noelvissers/esp32-smart-clock/hardware/smart-clock-library/3d-files/M3 Spacer Male-Female - 5mm Height x 3mm Thread.step

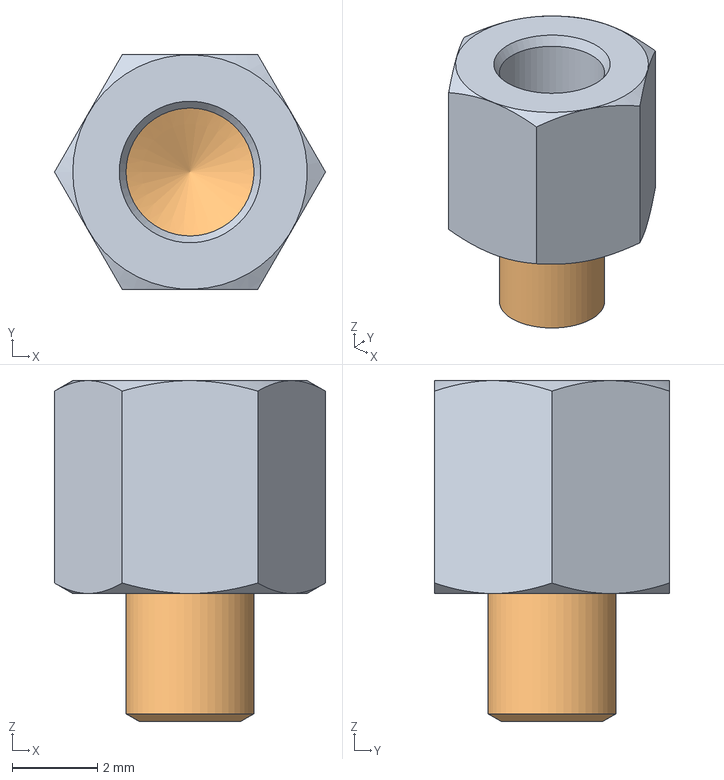
[picture p29: CAD file, 2020-08-22]
hardware/smart-clock-library/3d-files/M3 Spacer Male-Female - 5mm Height x 3mm Thread.step
6.36 x 5.51 x 8.00 mm
