noelvissers/esp32-smart-clock/hardware/smart-clock-library/3d-files/2x10 Male Pin Header Angle.STEP

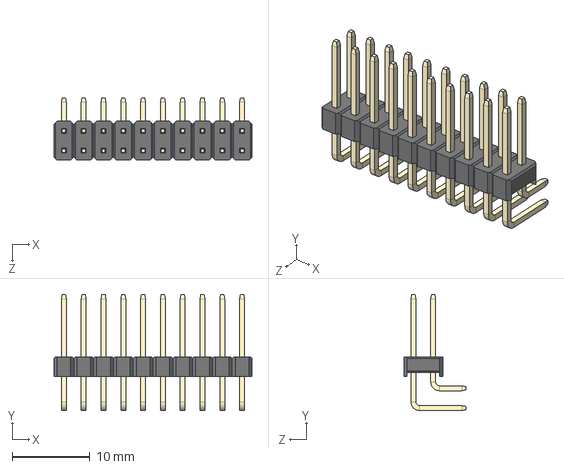
[picture p30: CAD file, 2020-08-22]
hardware/smart-clock-library/3d-files/2x10 Male Pin Header Angle.STEP
25.4 x 14.9 x 8.00 mm
