noelvissers/esp32-smart-clock/hardware/smart-clock-library/3d-files/1x5 Male Pin Header.STEP

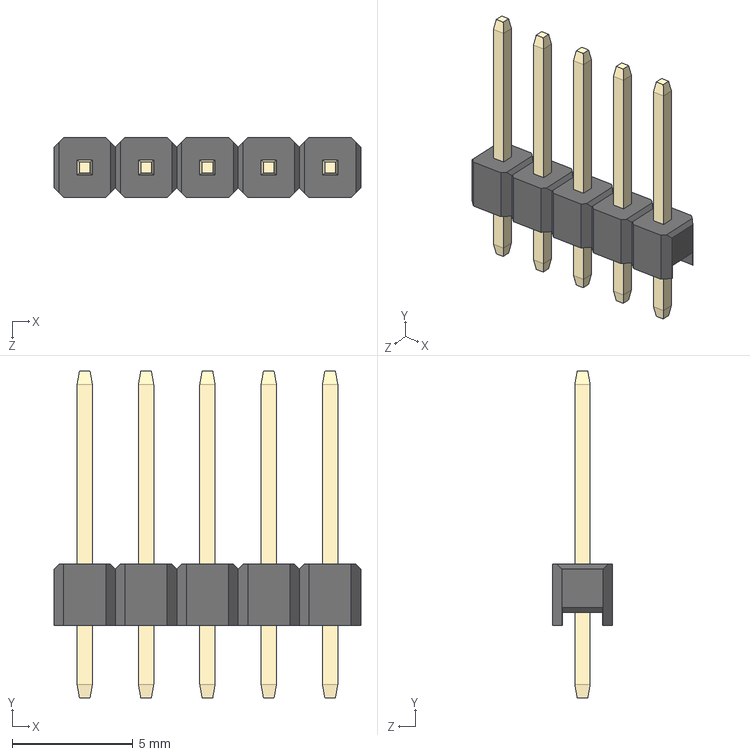
[picture p31: CAD file, 2020-08-22]
hardware/smart-clock-library/3d-files/1x5 Male Pin Header.STEP
12.7 x 13.5 x 2.50 mm
