noelvissers/esp32-smart-clock/hardware/smart-clock-library/3d-files/M3 Screw - 5mm.step

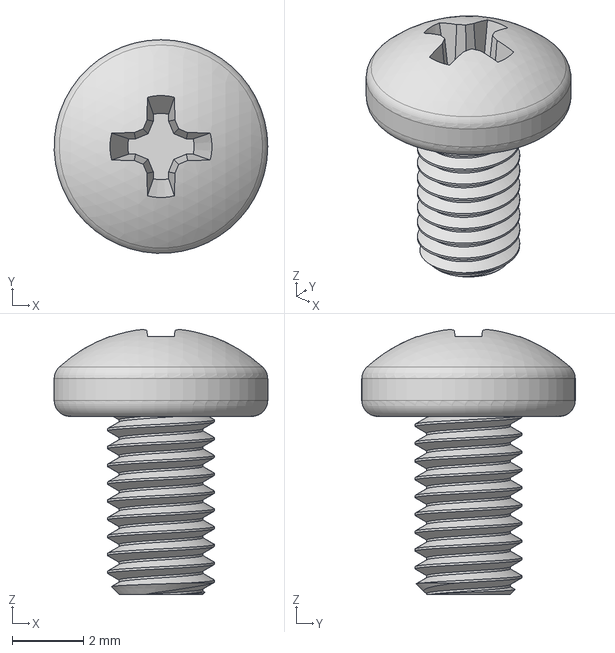
[picture p32: CAD file, 2020-08-22]
hardware/smart-clock-library/3d-files/M3 Screw - 5mm.step
6.00 x 6.00 x 7.44 mm
