noelvissers/esp32-smart-clock/src/pong.cpp

#include <Arduino.h>
#include "pong.h"
#include "display.h"
#include "config.h"

CDisplay PongDisplay;

unsigned int posBat = 4;      //1-6
unsigned int posBall_X = 7;   //0-15
unsigned int posBall_Y = 4;   //0-7
unsigned int speedBall = 250; //10-250
unsigned int speedBat = 75;   //delay in ms for bat to move
bool dirBall_X = 0;           //0 = Left, 1 = Right
bool dirBall_Y = 0;           //0 = Up, 1 = Down
bool wall = false;
long posWall = 2;
long lifeWall = 1;
unsigned int lastBallPosChange = 0;

unsigned long lastUp = 0;
unsigned long lastDown = 0;

void reset()
{
  posBat = 4;
  dirBall_X = 0;
  posBall_X = 7;
  posBall_Y = random(0, 7);
  speedBall = 200;
}

bool generateWall()
{
  long wallChance = random(0, 3); //1 in 3 to get a wall
  posWall = random(2, 7);
  lifeWall = random(1, 3);

  if (wallChance == 0)
    return true;
  else
    return false;
}

void CPong::start()
{
  Serial.println("[Pong] Starting...");

  for (;;)
  {
    //Check bat movement up
    if (_buttonPlusPressed && !_buttonMinPressed)
    {
      if ((millis() - lastUp) > speedBat)
      {
        posBat++;
        if (posBat > 6)
          posBat = 6;
        lastUp = millis();
      }
    }

    //Check bat movement down
    if (!_buttonPlusPressed && _buttonMinPressed)
    {
      if ((millis() - lastDown) > speedBat)
      {
        posBat--;
        if (posBat < 1)
          posBat = 1;
        lastDown = millis();
      }
    }

    //Check for exit button (select)
    if (_buttonSelectSet)
    {
      Serial.println("[Pong] Stopped...");
      _buttonSelectSet = false;
      break;
    }

    //Handle ball pos
    if ((millis() - lastBallPosChange) > speedBall)
    {
      lastBallPosChange = millis();

      if (!dirBall_X) //Left
      {
        posBall_X--;
        if (posBall_X == 0)
        {
          dirBall_X = 1;
          if (!wall)
          {
            wall = generateWall();
          }
          else
          {
            if (lifeWall <= 0)
              wall = false;
          }
        }
      }
      else //Right
      {
        posBall_X++;
      }

      if (!dirBall_Y) //Up
      {
        posBall_Y++;
        if (posBall_Y == 7)
          dirBall_Y = !dirBall_Y;
      }
      else //Down
      {
        posBall_Y--;
        if (posBall_Y == 0)
          dirBall_Y = !dirBall_Y;
      }

      //Check for loss
      if (posBall_X == 15)
      {
        //Ball is on the same line as bat, so you lost...
        PongDisplay.renderPongReset();
        reset();
      }

      //Check for bounce
      if (posBall_X == 14)
      {
        if (((posBall_Y - 1) == posBat) || (posBall_Y == posBat) || ((posBall_Y + 1) == posBat))
        {
          //Bounced
          dirBall_X = 0;
          speedBall = speedBall - 20;
          if (speedBall < 10 || speedBall > 1000)
            speedBall = 10;
        }
      }

      //Handle wall bounce
      if (wall && dirBall_X)
      {
        if ((posBall_X + 1) == posWall)
        {
          //Bounced
          dirBall_X = 0;
          lifeWall--;
        }
      }
    }

    //Draw pong
    PongDisplay.renderPong(posBat, posBall_X, posBall_Y, posWall, wall);
    delay(5);
  }
  reset();
}
